BCIT-BAJA/BCIT-BAJA/Hardware/sensorAmplifier/StrainAmplifierV1/AltiumLL/SamacSys_Images/3DM_6648.png

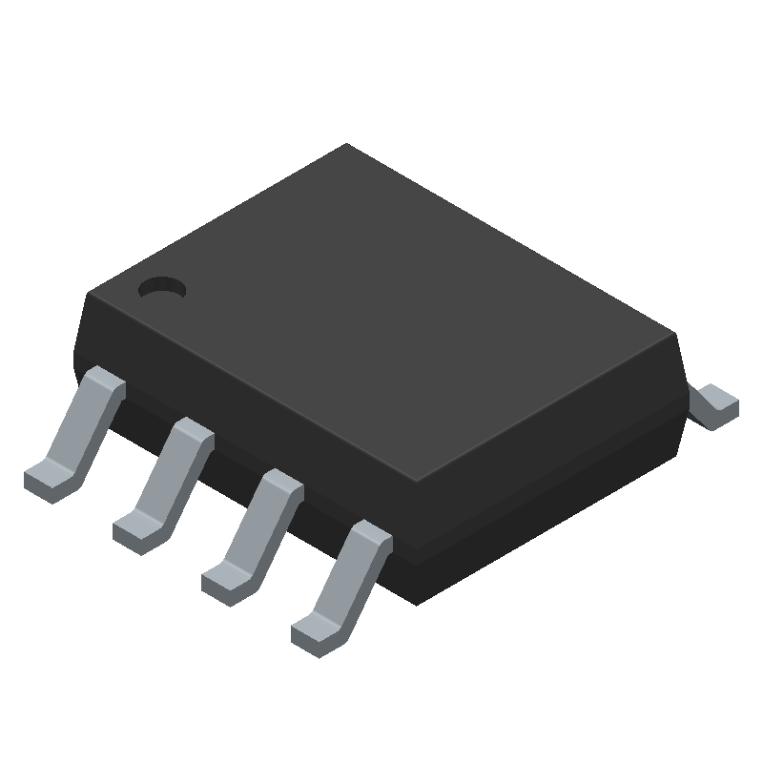
Hardware/sensorAmplifier/StrainAmplifierV1/AltiumLL/SamacSys_Images/3DM_6648.png
