BCIT-BAJA/BCIT-BAJA/Hardware/sensorAmplifier/StrainAmplifierV1/AltiumLL/SamacSys_Images/3DM_231006.png

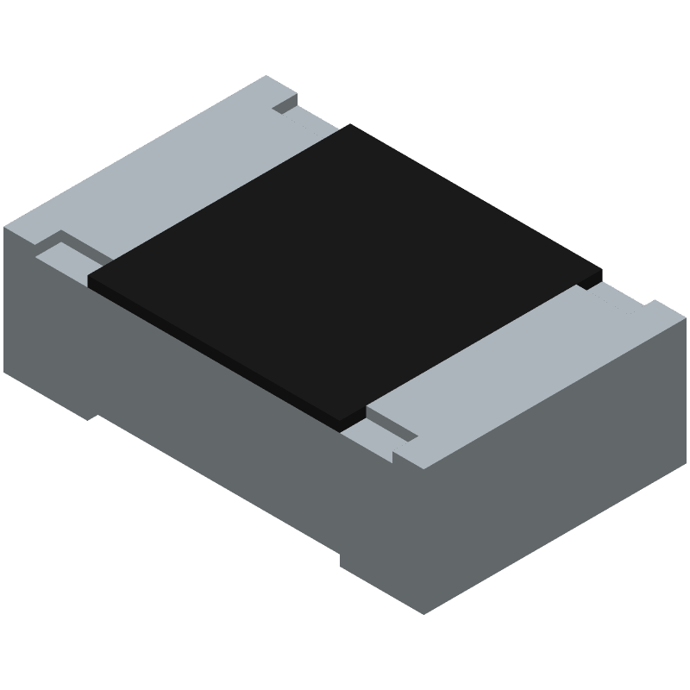
Hardware/sensorAmplifier/StrainAmplifierV1/AltiumLL/SamacSys_Images/3DM_231006.png
