BCIT-BAJA/BCIT-BAJA/Hardware/sensorAmplifier/StrainAmplifierV1/AltiumLL/SamacSys_Images/3DM_330383.png

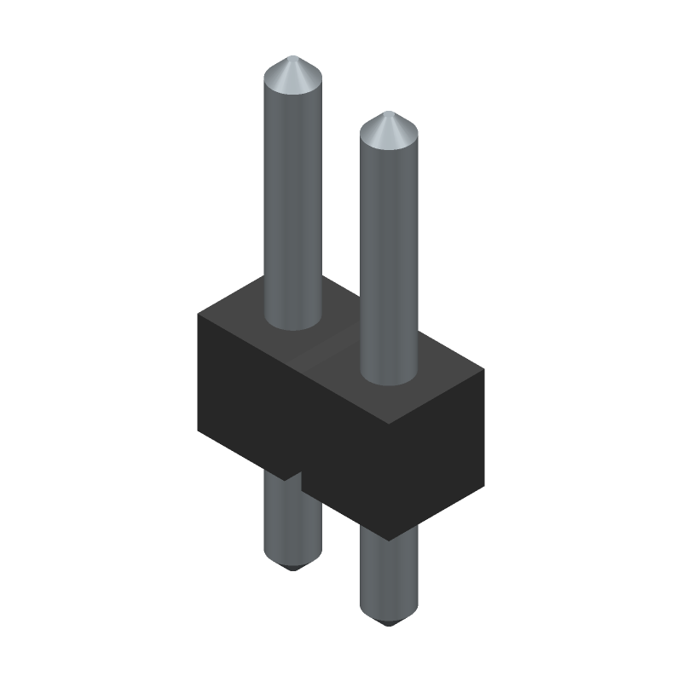
Hardware/sensorAmplifier/StrainAmplifierV1/AltiumLL/SamacSys_Images/3DM_330383.png
