BCIT-BAJA/BCIT-BAJA/Hardware/sensorAmplifier/StrainAmplifierV1/AltiumLL/SamacSys_Images/3DM_572694.png

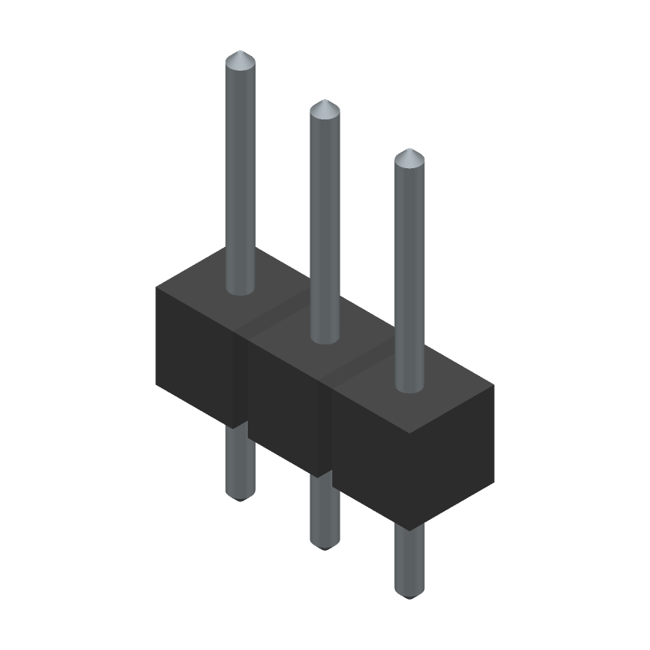
Hardware/sensorAmplifier/StrainAmplifierV1/AltiumLL/SamacSys_Images/3DM_572694.png
