BCIT-BAJA/BCIT-BAJA/Hardware/sensorAmplifier/StrainAmplifierV1/AltiumLL/SamacSys_Images/3DM_1516582.png

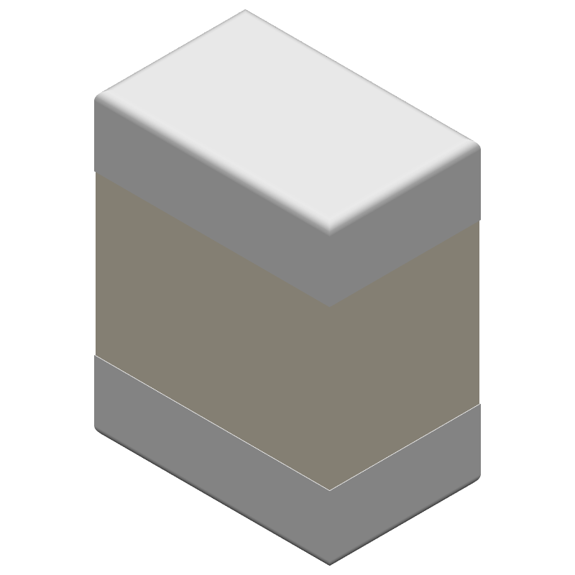
Hardware/sensorAmplifier/StrainAmplifierV1/AltiumLL/SamacSys_Images/3DM_1516582.png
