BCIT-BAJA/BCIT-BAJA/Hardware/Revision01/kicadImports/MIC5225-1.8YM5-TR/SOT-23-5_M5_MCH.step

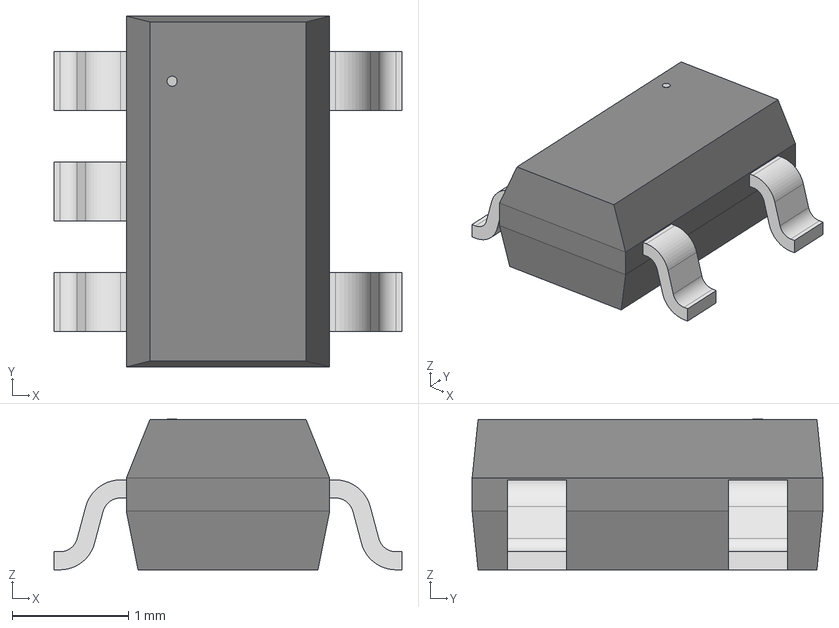
[picture p63: CAD file, 2025-06-12]
Hardware/Revision01/kicadImports/MIC5225-1.8YM5-TR/SOT-23-5_M5_MCH.step
3.00 x 3.02 x 1.30 mm
