BCIT-BAJA/BCIT-BAJA/Hardware/Revision01/kicadImports/MPU6500/MPU-6500.step

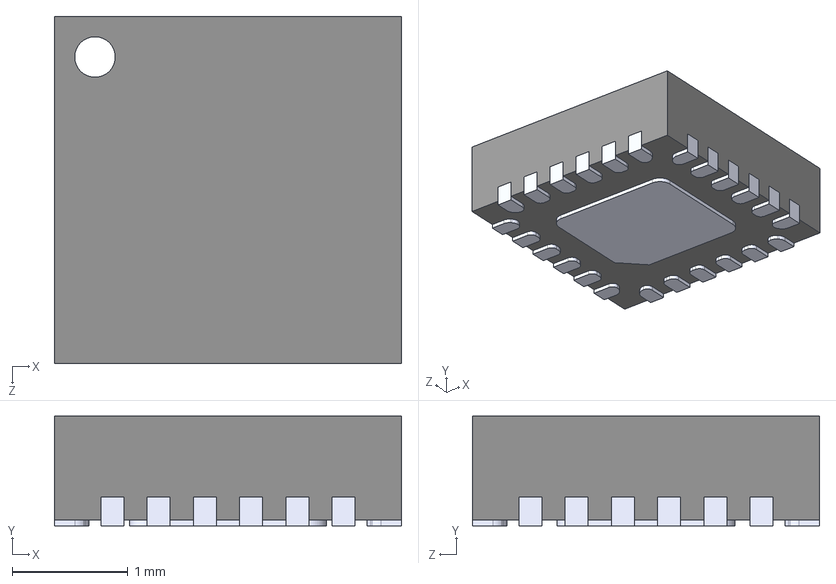
[picture p64: CAD file, 2025-07-13]
Hardware/Revision01/kicadImports/MPU6500/MPU-6500.step
3.00 x 0.95 x 3.00 mm
