BCIT-BAJA/BCIT-BAJA/Hardware/Revision01/kicadImports/NCP1117LPST50T3G/NCP1117LPST50T3G.step

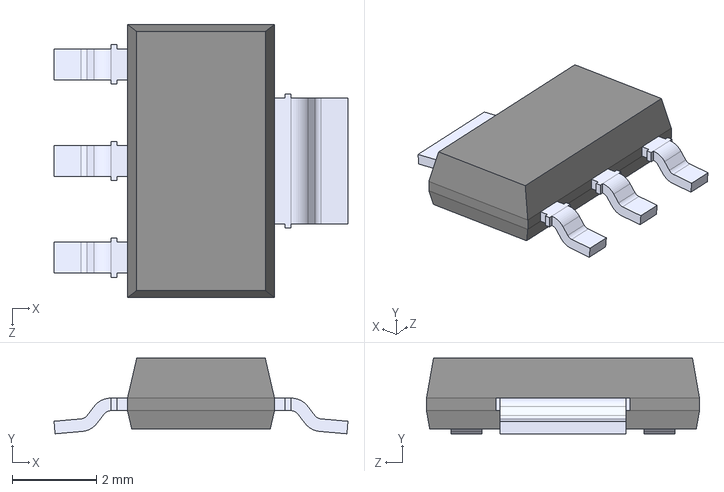
[picture p65: CAD file, 2025-03-31]
Hardware/Revision01/kicadImports/NCP1117LPST50T3G/NCP1117LPST50T3G.step
7.00 x 1.80 x 6.50 mm
