BCIT-BAJA/BCIT-BAJA/Hardware/Revision01/kicadImports/OSFW4BS8C1A/OSFW4BS8C1A (3)/OSFW4BS8C1A.step

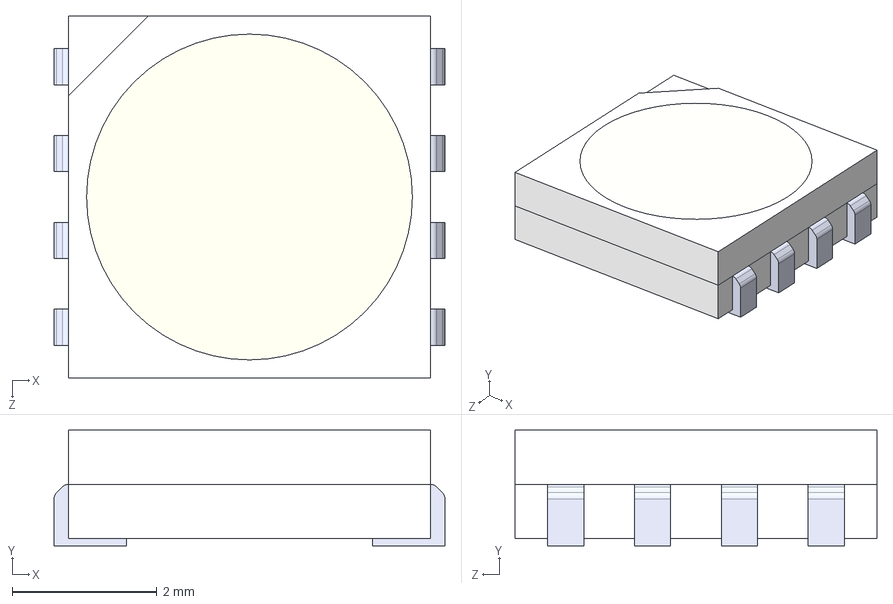
[picture p66: CAD file, 2025-05-16]
Hardware/Revision01/kicadImports/OSFW4BS8C1A/OSFW4BS8C1A (3)/OSFW4BS8C1A.step
5.40 x 1.60 x 5.00 mm
