BCIT-BAJA/BCIT-BAJA/Hardware/Revision01/kicadImports/OSFW4BS8C1A/QBLP679-RGBXW.step

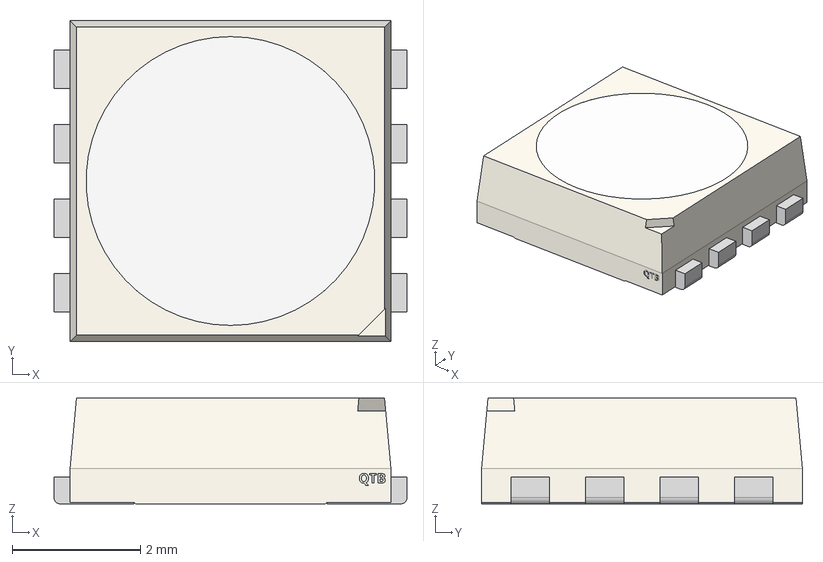
[picture p67: CAD file, 2025-05-16]
Hardware/Revision01/kicadImports/OSFW4BS8C1A/QBLP679-RGBXW.step
5.50 x 5.00 x 1.65 mm
