BCIT-BAJA/BCIT-BAJA/Hardware/Revision01/kicadImports/T520V686M010ATE045-68uF-BC/CTS_TCM2NOBNOKBOPT_7343_L7.6W4.6H1.9T0.13S1.3F2.5A3.6X0.05.step

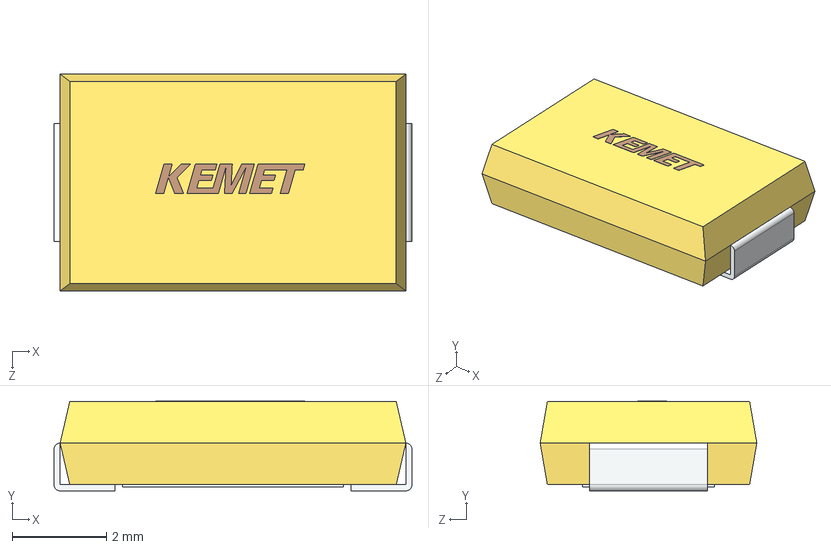
[picture p68: CAD file, 2025-03-11]
Hardware/Revision01/kicadImports/T520V686M010ATE045-68uF-BC/CTS_TCM2NOBNOKBOPT_7343_L7.6W4.6H1.9T0.13S1.3F2.5A3.6X0.05.step
7.60 x 1.91 x 4.60 mm
