BCIT-BAJA/BCIT-BAJA/Hardware/Revision01/kicadImports/TPS629203QDRLRQ1/DRL0008A.stp

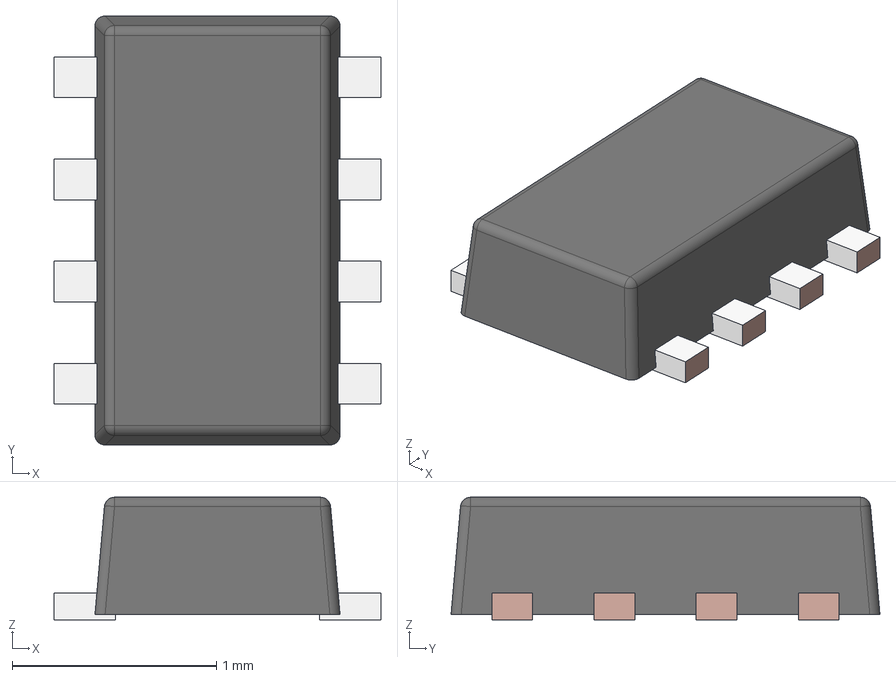
[picture p69: CAD file, 2025-06-18]
Hardware/Revision01/kicadImports/TPS629203QDRLRQ1/DRL0008A.stp
1.60 x 2.10 x 0.6 mm
FRAME-DRL0008A
BODY-SOT
