BCIT-BAJA/BCIT-BAJA/Hardware/Revision01/kicadImports/VLS3012CX_2R2M_1/VLS3012CX-2R2M-1.step

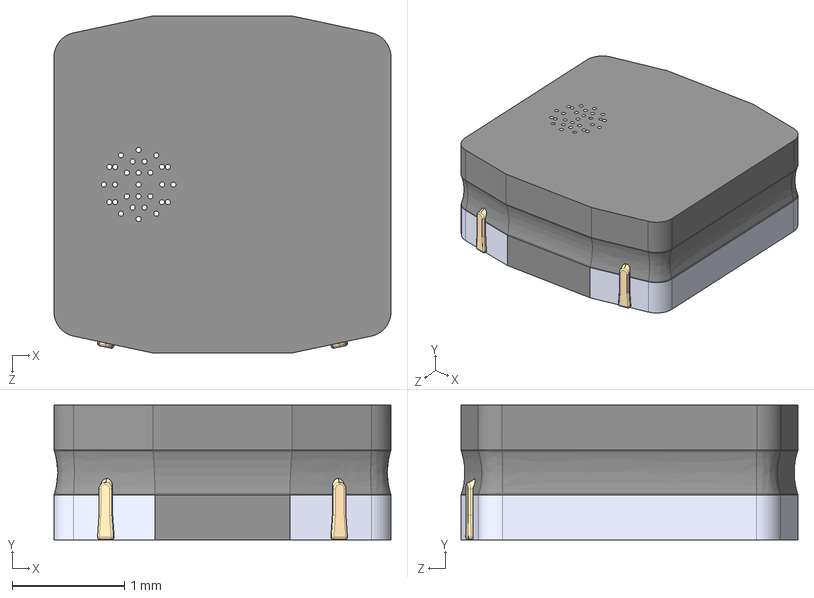
[picture p70: CAD file, 2025-06-18]
Hardware/Revision01/kicadImports/VLS3012CX_2R2M_1/VLS3012CX-2R2M-1.step
3.00 x 1.20 x 3.00 mm
