BCIT-BAJA/BCIT-BAJA/Hardware/Revision01/kicadImports/VLS5045EX_151M_H/VLS5045EX-151M-H.step

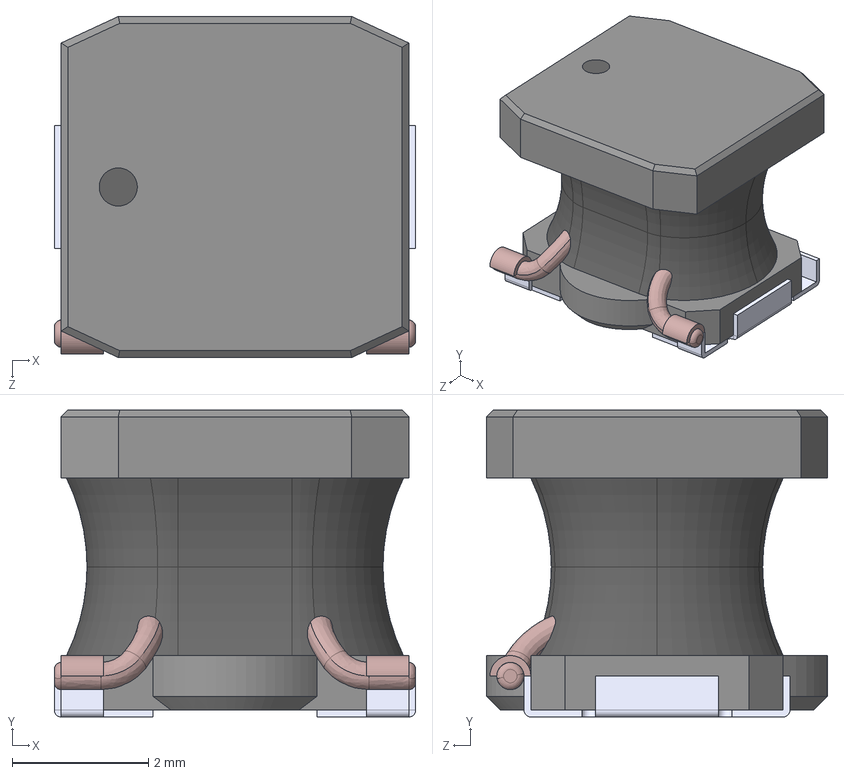
[picture p71: CAD file, 2025-06-25]
Hardware/Revision01/kicadImports/VLS5045EX_151M_H/VLS5045EX-151M-H.step
5.30 x 4.50 x 5.00 mm
