BCIT-BAJA/BCIT-BAJA/Hardware/sensorAmplifier/StrainAmplifierV1/Imports/TLV9062IDDFR/AltiumDesigner/SOT_62IDDFR_TEX.step

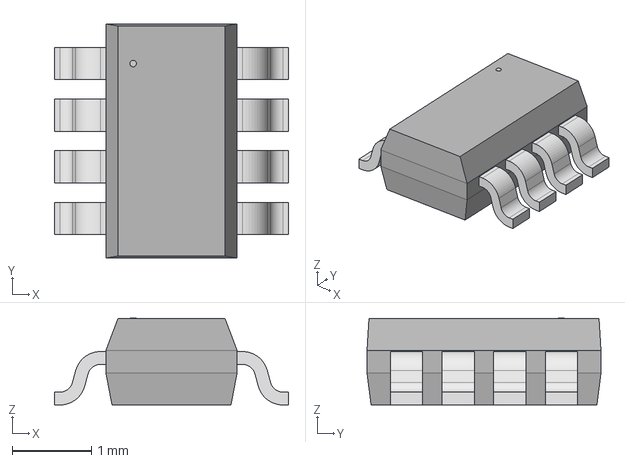
[picture p72: CAD file, 2025-05-21]
Hardware/sensorAmplifier/StrainAmplifierV1/Imports/TLV9062IDDFR/AltiumDesigner/SOT_62IDDFR_TEX.step
2.95 x 2.95 x 1.09 mm
