BCIT-BAJA/BCIT-BAJA/Hardware/sensorAmplifier/StrainAmplifierV1/Imports/TLV9062IDDFR/DDF0008A.stp

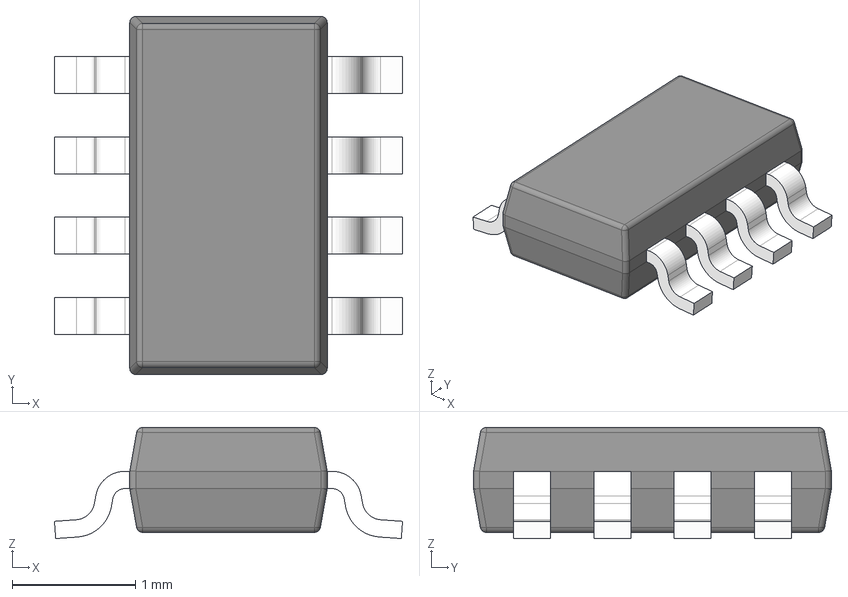
[picture p73: CAD file, 2025-05-21]
Hardware/sensorAmplifier/StrainAmplifierV1/Imports/TLV9062IDDFR/DDF0008A.stp
2.82 x 2.90 x 0.9 mm
BODY-SO
LEAD-SO x 8
PIN1-ID
