BCIT-BAJA/BCIT-BAJA/Hardware/sensorAmplifier/StrainAmplifierV1/PCB1_AmplifierBoard.step

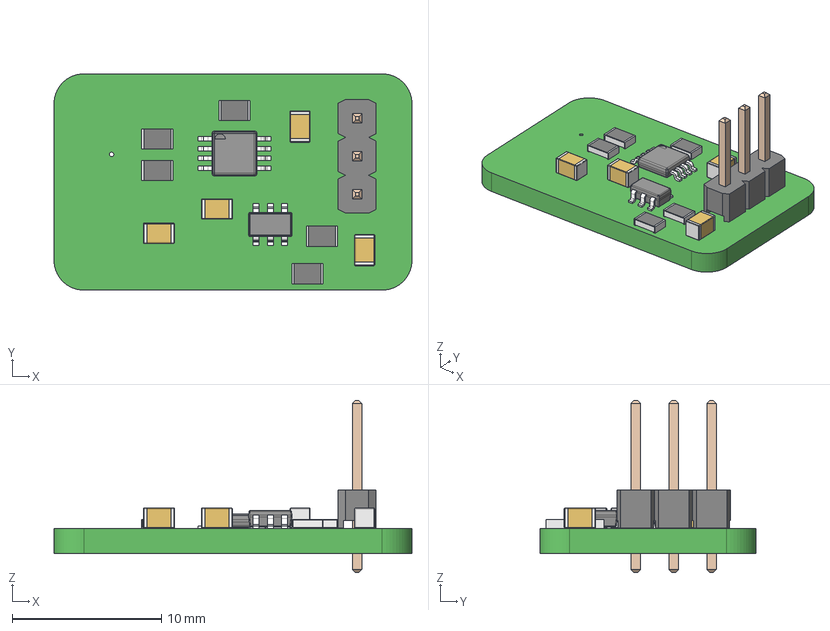
[picture p74: CAD file, 2025-07-02]
Hardware/sensorAmplifier/StrainAmplifierV1/PCB1_AmplifierBoard.step
24.0 x 14.5 x 11.5 mm
6130xx11121_PIN x 3
Mid Body x 5
Mark x 5
BODY_MUY08A
LEAD_MUY08A x 8
EXP_PAD_MUY08A
BODY-SOT
LEAD-SOT x 6
