BCIT-BAJA/BCIT-BAJA/Hardware/sensorAmplifier/StrainAmplifierV1_Kicad/StrainAmplifierV1/imports/TLV9061SQDBVRQ1/DBV0006A.stp

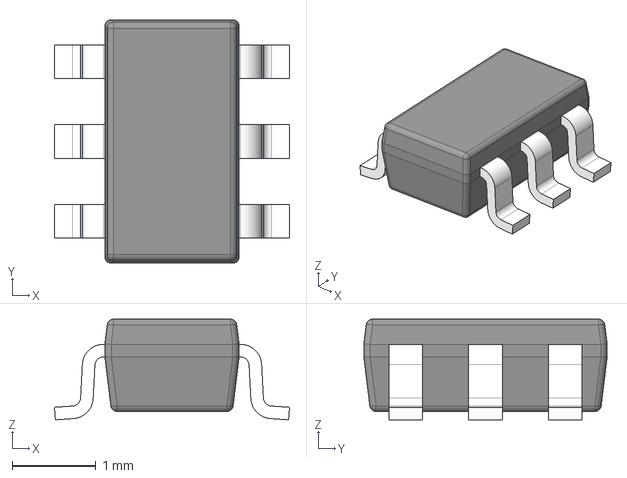
[picture p75: CAD file, 2025-06-21]
Hardware/sensorAmplifier/StrainAmplifierV1_Kicad/StrainAmplifierV1/imports/TLV9061SQDBVRQ1/DBV0006A.stp
2.80 x 2.90 x 1.20 mm
BODY-SOT
LEAD-SOT x 6
