BCIT-BAJA/BCIT-BAJA/Hardware/sensorAmplifier/StrainAmplifierV1/AltiumLL/Temp/NE555DR.stp

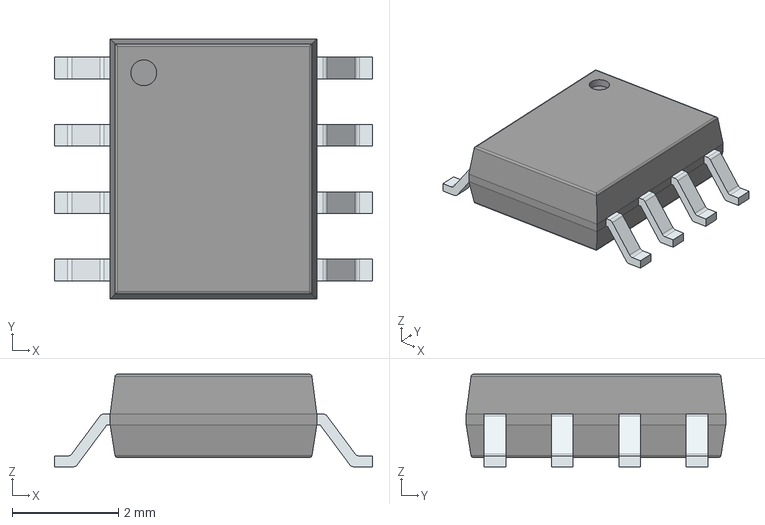
[picture p76: CAD file, 2025-05-27]
Hardware/sensorAmplifier/StrainAmplifierV1/AltiumLL/Temp/NE555DR.stp
6.00 x 4.90 x 1.75 mm
PinsArrayLR
