BCIT-BAJA/BCIT-BAJA/Hardware/sensorAmplifier/StrainAmplifierV1/AltiumLL/Temp/RNCS0805BKE100K.stp

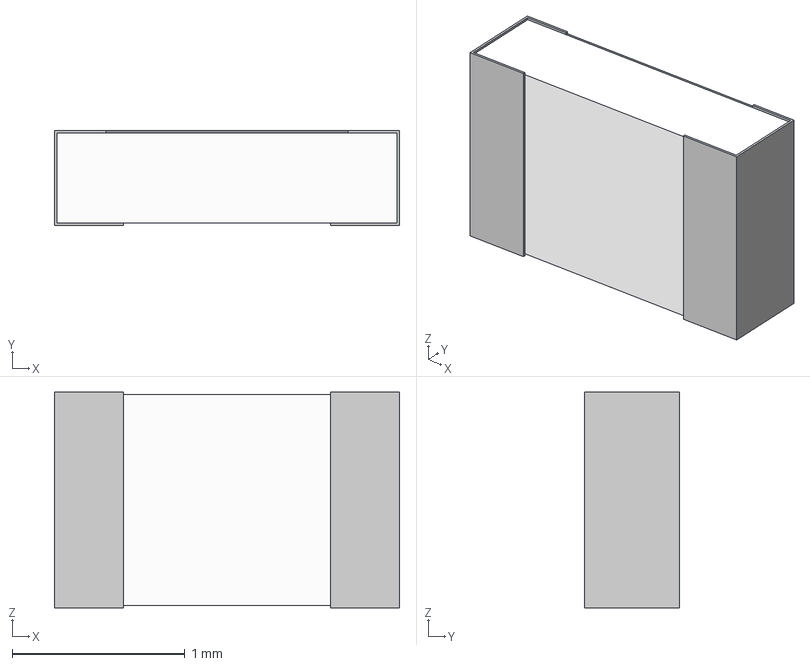
[picture p77: CAD file, 2025-05-27]
Hardware/sensorAmplifier/StrainAmplifierV1/AltiumLL/Temp/RNCS0805BKE100K.stp
2.00 x 0.55 x 1.25 mm
