BCIT-BAJA/BCIT-BAJA/testing/LTSPICE_SIMS/Draft2.asc

D1: schottky
M1: pmos
R1: res; 1
RL: res; 1K
V1: voltage; 0
V2: voltage; 4.2
Named nets: +USB_C, 0, +V_batt, V_out
.tran 100MS
