BCIT-BAJA/BCIT-BAJA/testing/LTSPICE_SIMS/amplifierClamped.asc

C1: cap; 10nF
R1: res; 1.6K
R2: res; 1K
R3: res; 1K
R4: res; 1K
R5: res; 150K
R6: res; 120K
U1: DDZ9684
U2: DDZ9684
U3: INA317
U4: TLV9062
V2: voltage; 3.3
V3: voltage; 5
V4: voltage; 2.5
V5: voltage; SINE(2.5 0.015 1K)
Named nets: 0, Vout, Vref, strain_D-, strain_D+, +StrainPWR
.lib library\\DDZ9684.LIB
Vz
Nominal 3.3V
Min 3.13V
Max 3.47
.tran 2ms
