BCIT-BAJA/BCIT-BAJA/testing/LTSPICE_SIMS/clampingDiodesCircuit.asc

C1: cap; 100nF
R1: res; 5K
U1: DDZ9684
U2: DDZ9684
V1: voltage; SINE(1.6666 5 1000); AC 1
V2: voltage; 3.3
Named nets: 0, Vout, Vin
.lib library\\DDZ9684.LIB
Vz
Nominal 3.3V
Min 3.13V
Max 3.47
.ac dec 100 1 10K
