BCIT-BAJA/BCIT-BAJA/testing/LTSPICE_SIMS/PMOS_switchingStrainV.asc

C1: cap; 100µF
M1: pmos; ZXMP10A18G
R1: res; 10K
R2: res; 350
R3: res; 350
R4: res; 350
R5: res; 355
R6: res; 1
R10: res; 350
R11: res; 350
R12: res; 350
R13: res; 350
R14: res; 350
R15: res; 350
R16: res; 350
R17: res; 350
R18: res; 350
R19: res; 350
R20: res; 350
R21: res; 350
R22: res; 350
R23: res; 350
R24: res; 350
R25: res; 350
R26: res; 350
R27: res; 350
R28: res; 350
R29: res; 350
R30: res; 350
R31: res; 350
R32: res; 350
R33: res; 350
R34: res; 350
R35: res; 350
R36: res; 350
R37: res; 350
V1: voltage; 5
V2: voltage; PULSE(0 3.3 0 0.1us 0.1us 0.5ms 1ms)
Named nets: 0, StrainV+, StrainV-, EN, strainD+, strainD-
.lib library\\INA317.LIB
.lib library\\tlv9062.LIB
.lib library\\INA333.LIB
.tran 0 4ms 0 1us
