BCIT-BAJA/BCIT-BAJA/testing/LTSPICE_SIMS/Draft1.asc

C1: cap; 1µF
C2: cap; 0.1µF
C4: cap; 10µF
C5: cap; 1µF
L1: ind; 150µH
R1: res; 76.8K
R2: res; 10K
U1: LMR51606YF_TRANS
V1: voltage; 15
Named nets: 0, Vout
.lib C:\\Users\\Parry\\Documents\\BCIT-BAJA\\testing\\LTSPICE_SIMS\\library\\LMR51606YF_trans.lib
.tran 1
Failed attempt. MODEL is used only for Pspice
