BCIT-BAJA/BCIT-BAJA/testing/LTSPICE_SIMS/powerSupplyMeasurement.asc

M1: nmos; Si5515_N
M3: pmos; Si4451DY
R1: res; 10K
R2: res; 10K
R3: res; 1.5K
R4: res; 330
V1: voltage; SINE(11 5 1)
V2: voltage; PULSE(0 3.3 3 0.1u 0.1 2 3)
Named nets: 0, Enable, BatteryVoltage, BatteryMeasurement
.tran 25
Test INPUTS:
changed battery voltage from 6V, 16V
Checked to see enable enables battery measurement circuit on and Off
