BCIT-BAJA/BCIT-BAJA/testing/LTSPICE_SIMS/strainAmplifier.asc

R1: res; 1Meg
R2: res; 200K
R3: res; 100K
R6: res; 1K
U1: TLV9062
U3: INA317
V3: voltage; SINE(2.5 0.015 1K)
V4: voltage; 2.5
V5: voltage; 3.3
V6: voltage; 4.996
Named nets: Strain_D+, Strain_D-, StrainV_PWR, 0, 3.3V, Vref, V_strainOut
.lib library\\INA317.LIB
.lib library\\tlv9062.LIB
.lib library\\INA333.LIB
.tran 0 2ms 0 1us
.lib library\\DDZ9684.LIB
