BCIT-BAJA/BCIT-BAJA/testing/LTSPICE_SIMS/strainGaugeTransientAnalysis.asc

C1: cap; 10nF
C2: cap; 100µF
C3: cap; 0.1µF
D1: diode
M1: pmos; Si7137DP
R1: res; 10k
R2: res; 350
R3: res; 350
R4: res; 350
R5: res; 355
R6: res; 1K
R7: res; 100K
R8: res; 200K
R9: res; 1.6K
R10: res; 350
R11: res; 350
R12: res; 350
R13: res; 350
R14: res; 350
R15: res; 350
R16: res; 350
R17: res; 350
R18: res; 350
R19: res; 350
R20: res; 350
R21: res; 350
R22: res; 350
R23: res; 350
R24: res; 350
R25: res; 350
R26: res; 350
R27: res; 350
R28: res; 350
R29: res; 350
R30: res; 350
R31: res; 350
R32: res; 350
R33: res; 350
R34: res; 350
R35: res; 350
R36: res; 350
R37: res; 350
U1: DDZ9684
U3: INA333
U4: DDZ9684
V1: voltage; 10
V2: voltage; PULSE(0 3.3 1ms 1us 1us 0 400ms 3)
V3: voltage; SINE(2.5 0.015 1K)
V4: voltage; 2.5
V5: voltage; 3.3
V6: voltage; 5
Named nets: 0, Strain_D+, Strain_D-, StrainV_PWR, ADC_IN, Vref, 3.3V, 5V
.lib library\\INA317.LIB
.lib library\\tlv9062.LIB
.lib library\\INA333.LIB
.lib library\\DDZ9684.txt
.tran 0 10ms 0 1us
