BCIT-BAJA/BCIT-BAJA/testing/LTSPICE_SIMS/RC_TimeConstantForADC.asc

C1: cap; 100nF; V=6
R1: res; 10K
V1: voltage; PULSE(0 3.3 0 1n 1n 1 2)
Named nets: 0, Vout
.tran 5m
